Squantor/selfMixingLaserRanger/hardware/laserRangerExploration/laserRangerExploration.sch

## KiCad design hardware/laserRangerExploration/laserRangerExploration.sch (2019-06-06)

Schematic: laserRangerExploration.sch

Parts:
N1: OHWLOGO; OSHW-Symbol_6.7x6mm_SilkScreen
N2: 20190606; Label_version
